Moragor/BatteryAnalyzer_MkII/tables and graphs/100mA_mWh.png

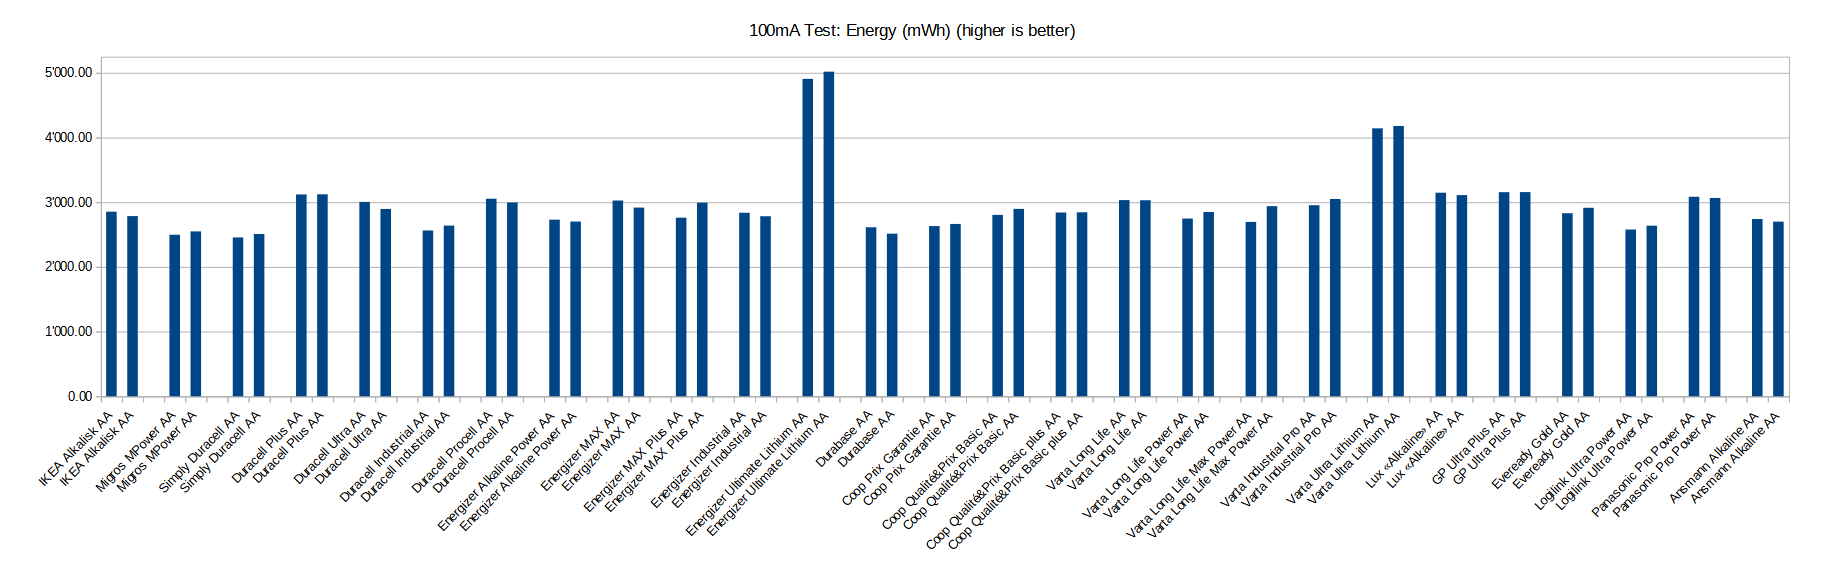
tables and graphs/100mA_mWh.png
