Moragor/BatteryAnalyzer_MkII/tables and graphs/500mA_mWh.png

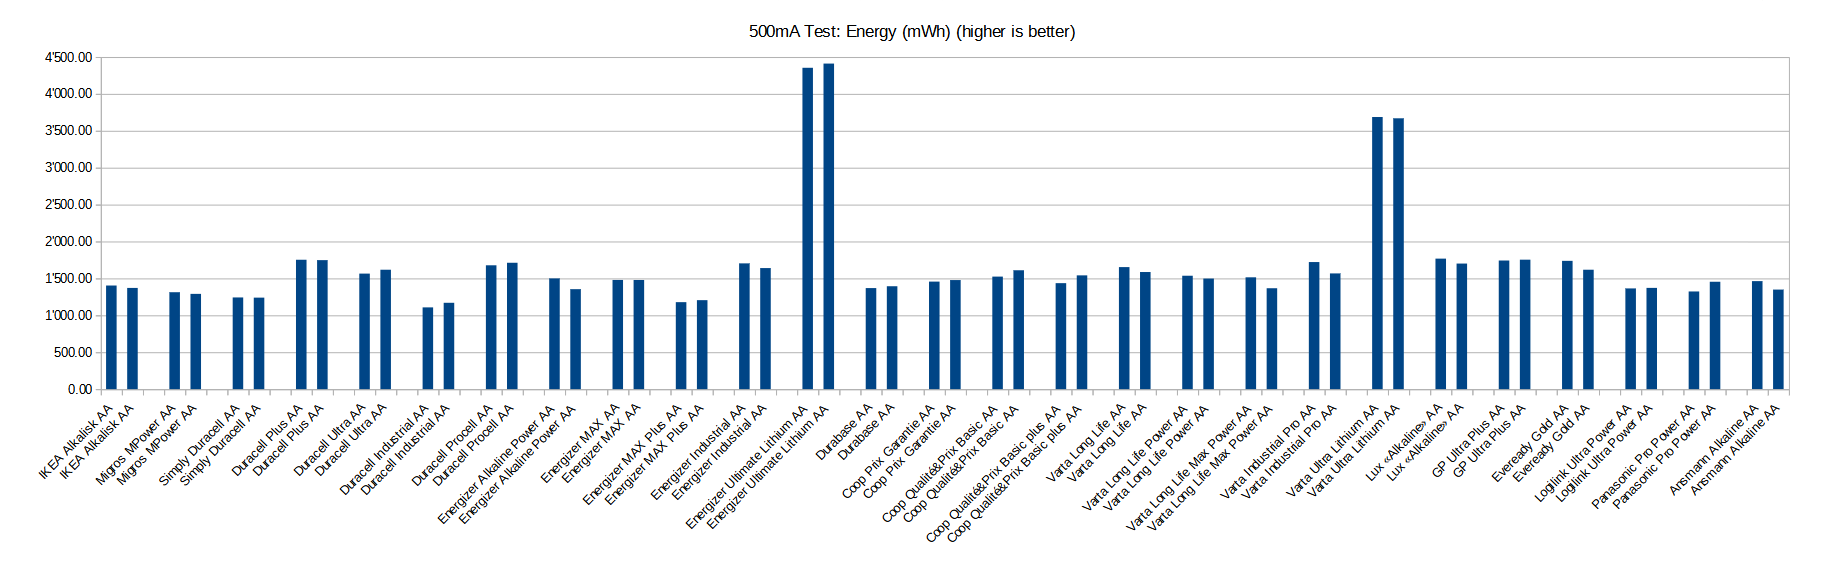
tables and graphs/500mA_mWh.png
