Moragor/BatteryAnalyzer_MkII/tables and graphs/500mA_PpmWh.png

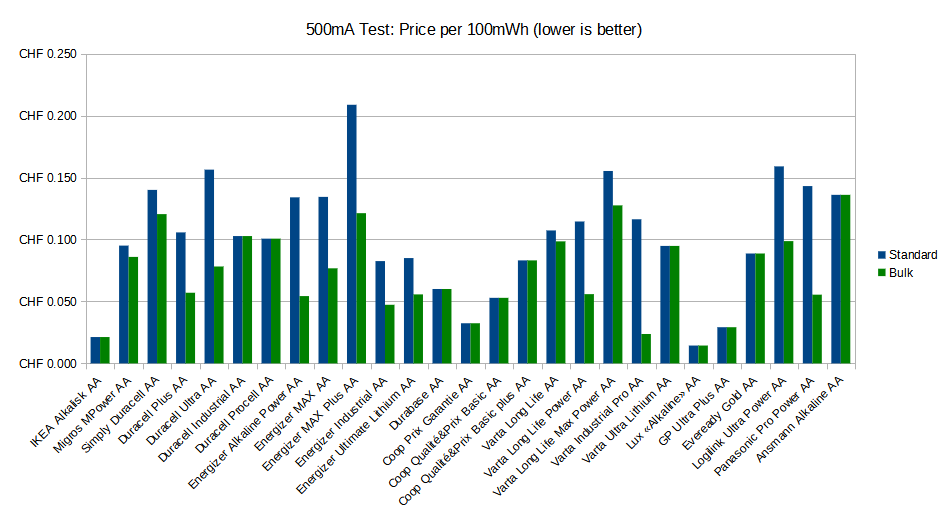
tables and graphs/500mA_PpmWh.png
