Moragor/BatteryAnalyzer_MkII/tables and graphs/500mA_Score.png

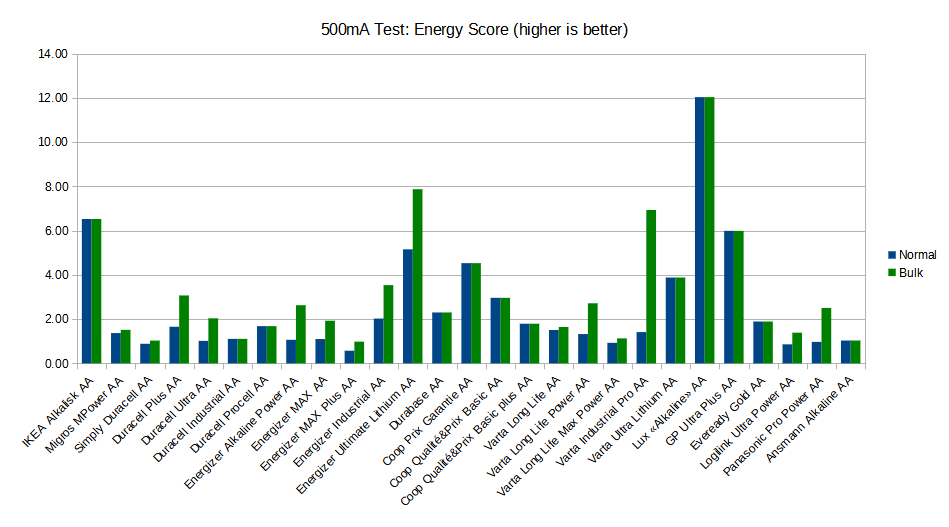
tables and graphs/500mA_Score.png
