Moragor/BatteryAnalyzer_MkII/tables and graphs/Discharge_curve_500mA.png

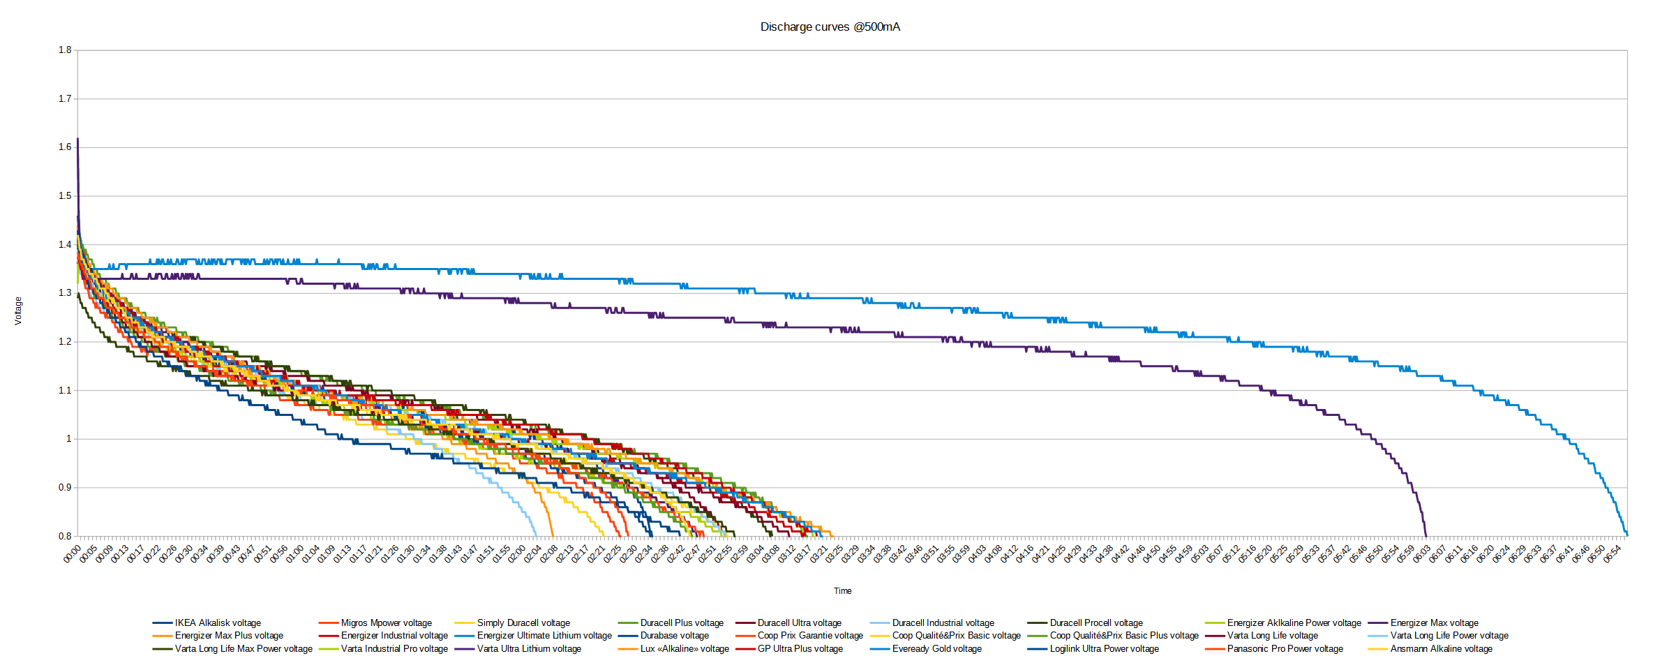
tables and graphs/Discharge_curve_500mA.png
