Moragor/BatteryAnalyzer_MkII/tables and graphs/High_drain_loss.png

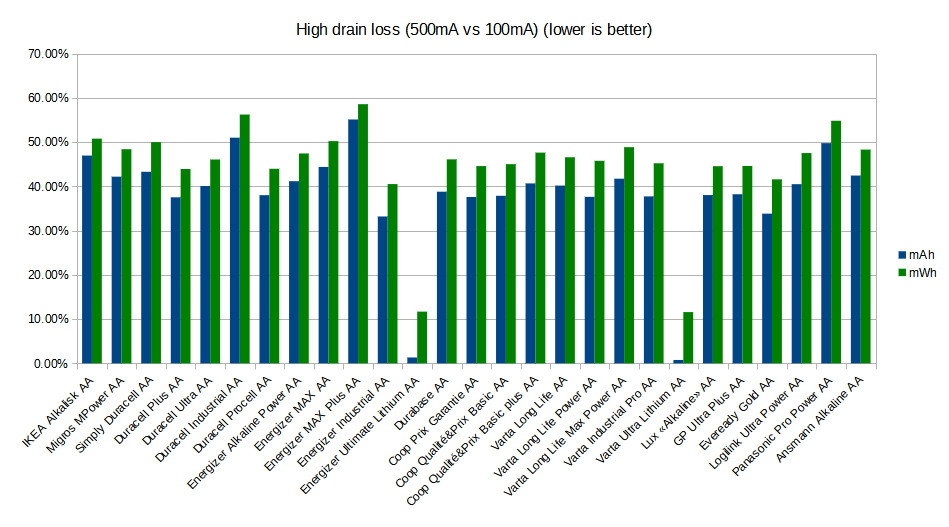
tables and graphs/High_drain_loss.png
